stevfu/elec4450-project/Pictures/Inductor Current.png

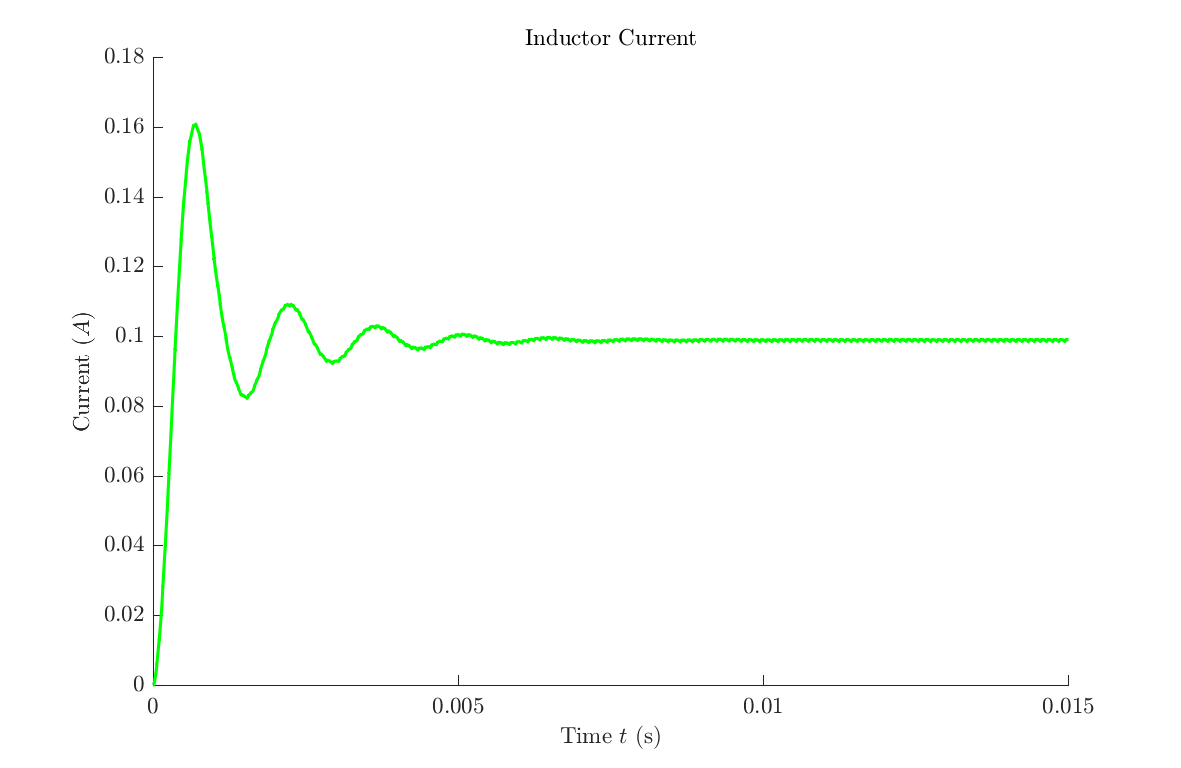
Pictures/Inductor Current.png
